zsdycs/ginpun/kb84/1. 成品图片/KB84-1.jpg

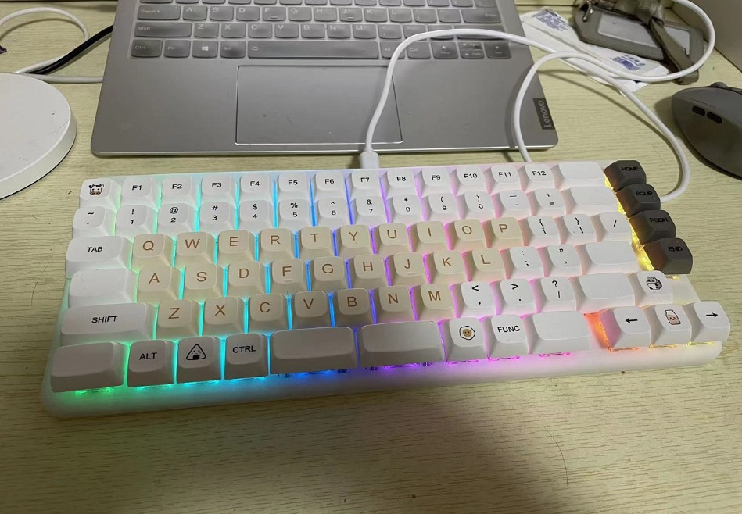
kb84/1. 成品图片/KB84-1.jpg
