zsdycs/ginpun/kb84/1. 成品图片/KB84-2.jpg

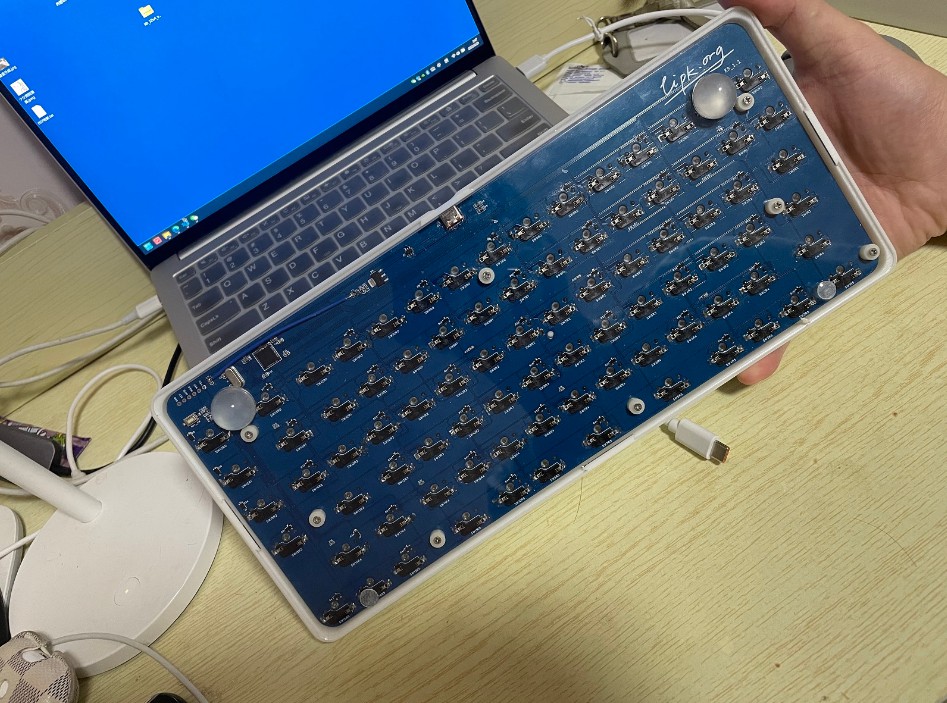
kb84/1. 成品图片/KB84-2.jpg
