zsdycs/ginpun/kb84/1. 成品图片/KB84-5.jpg

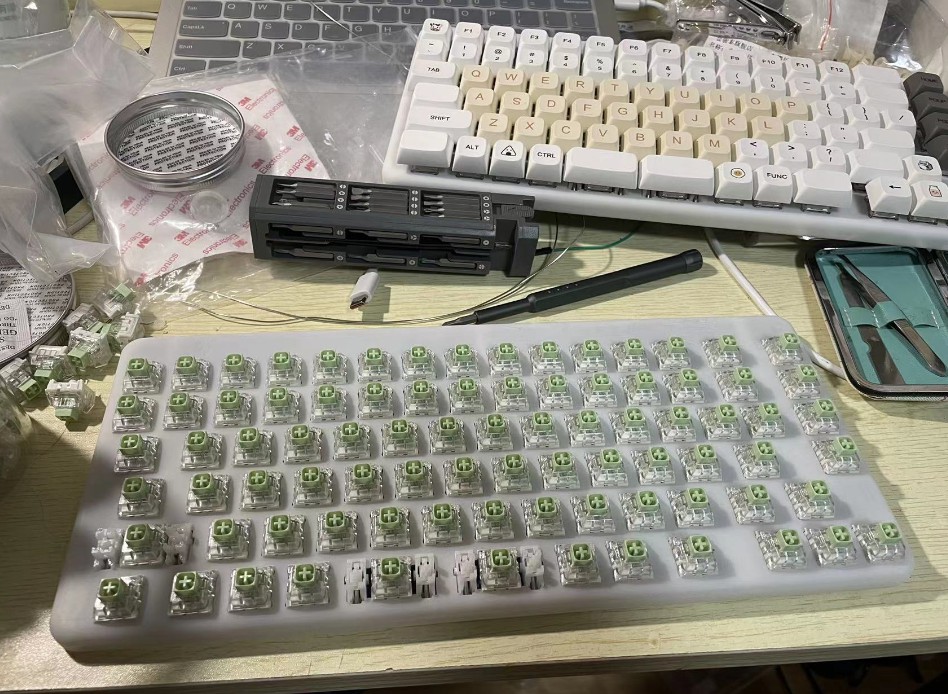
kb84/1. 成品图片/KB84-5.jpg
