zsdycs/ginpun/kb84/3. 原理图/SCH_kb_32u4_v1.3_P2.png

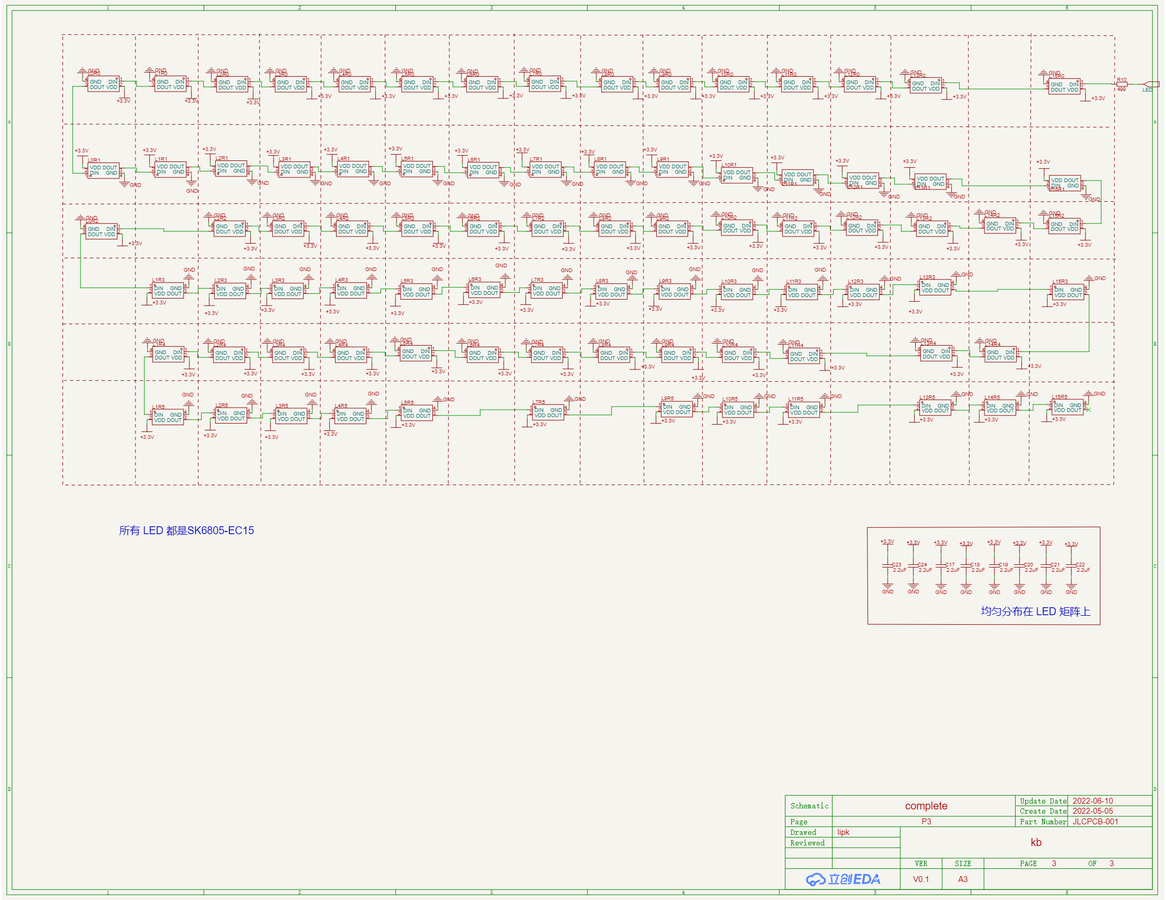
kb84/3. 原理图/SCH_kb_32u4_v1.3_P2.png
