zsdycs/ginpun/kb84/4. 电路板/kb_32u4_v1.3_top.png

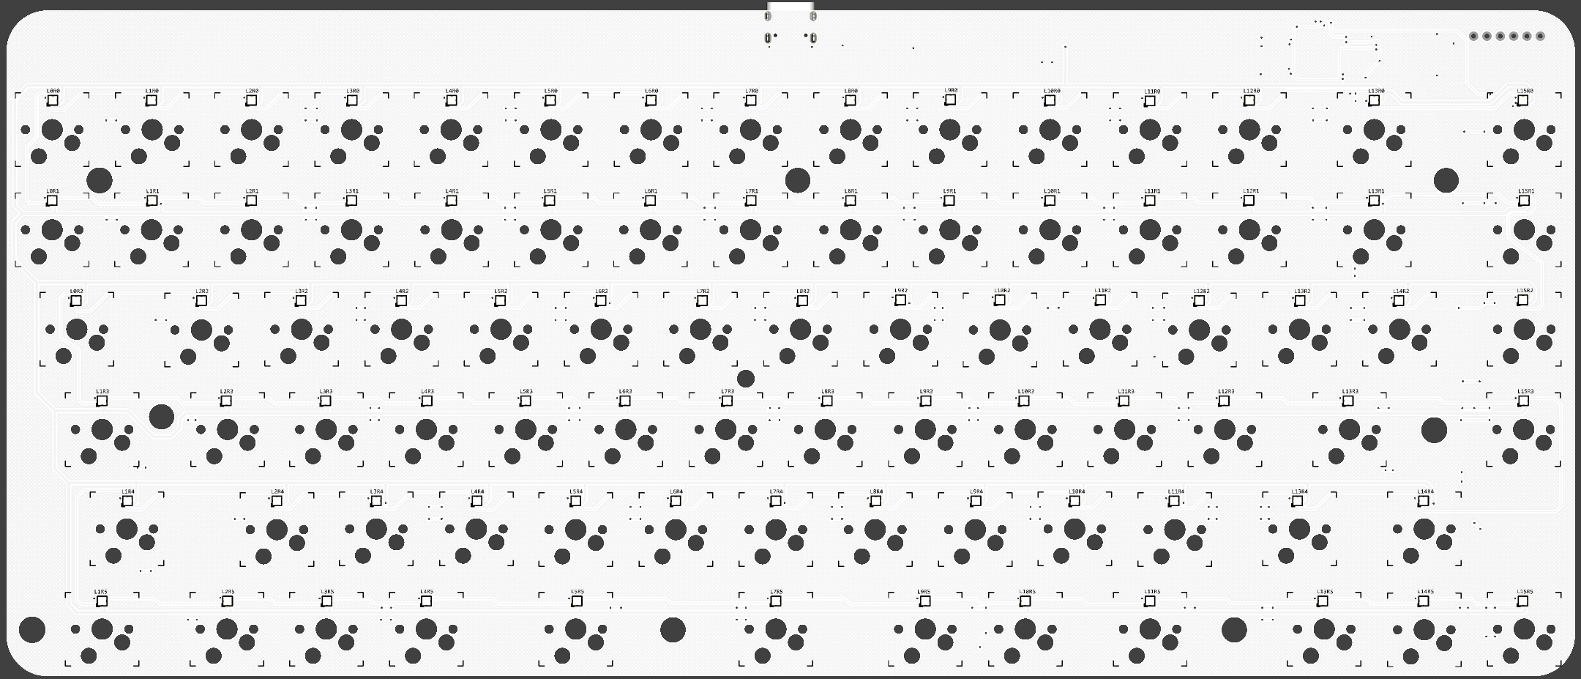
kb84/4. 电路板/kb_32u4_v1.3_top.png
