zsdycs/ginpun/kb84/键盘设计文件/keyboard-Layer 1.jpg

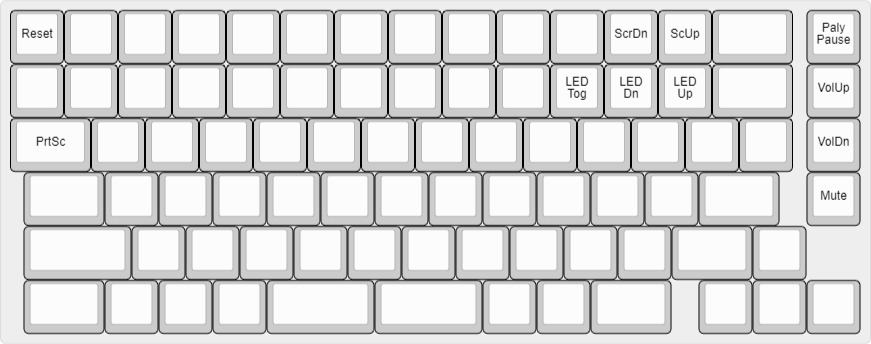
kb84/键盘设计文件/keyboard-Layer 1.jpg
