zsdycs/ginpun/kb84/键盘设计文件/键盘矩阵布线.jpg

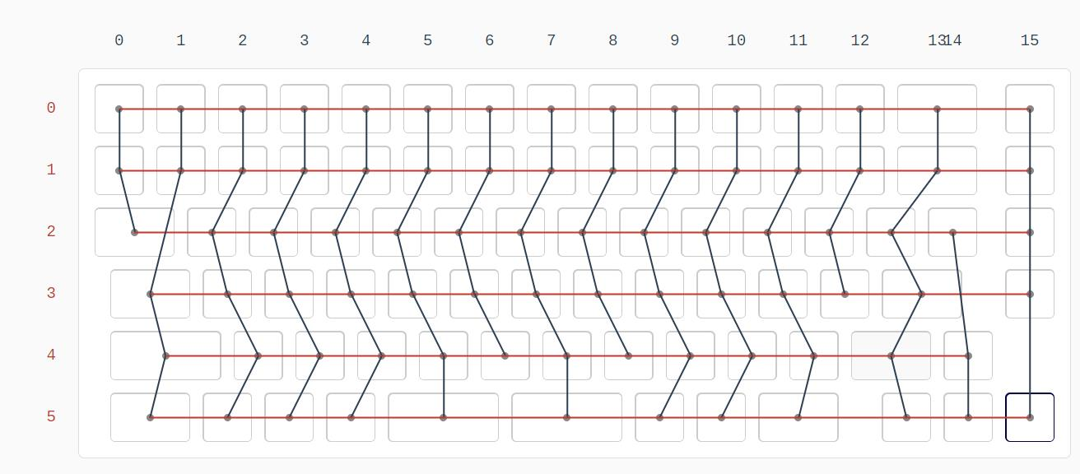
kb84/键盘设计文件/键盘矩阵布线.jpg
