zsdycs/ginpun/sg_v2/4. 电路板/PCB_buttom.png

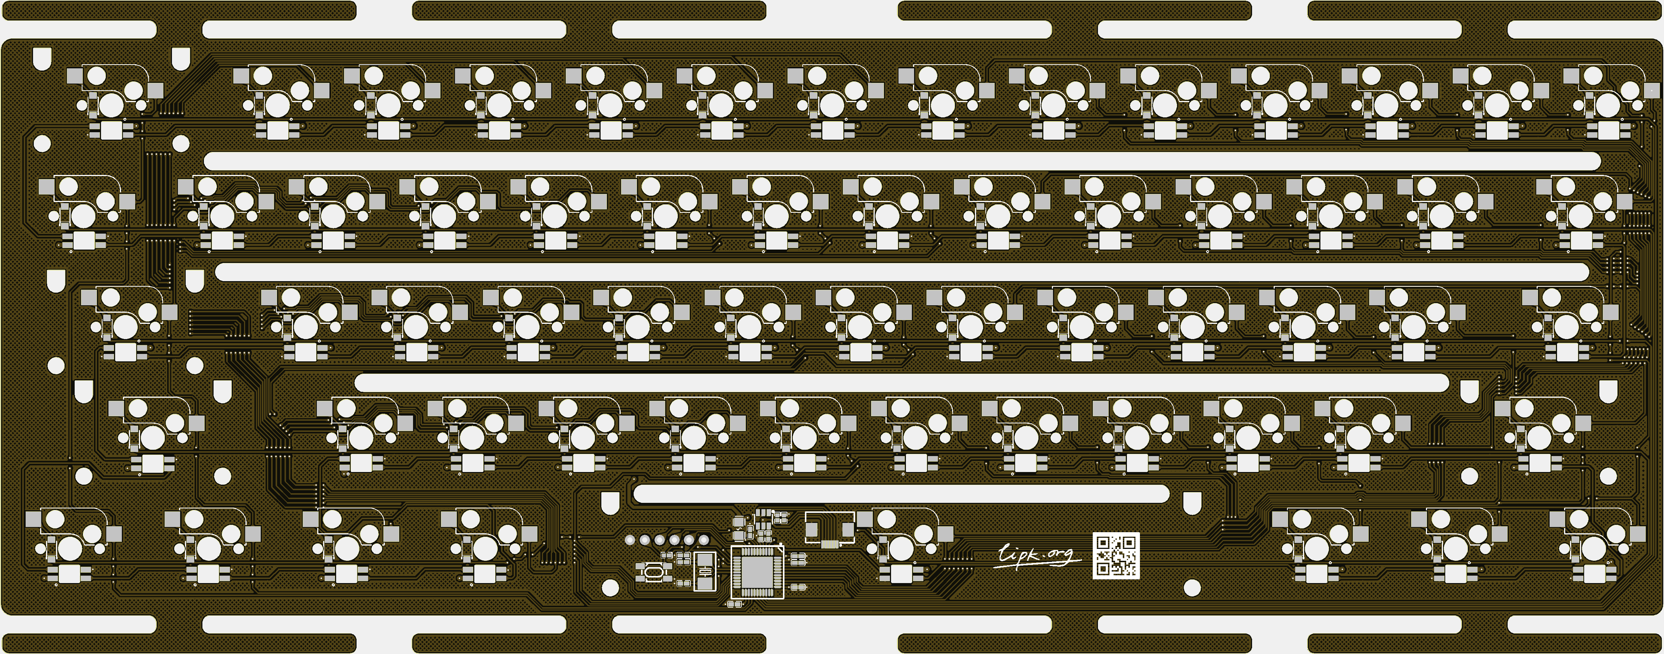
sg_v2/4. 电路板/PCB_buttom.png
