zsdycs/ginpun/sg_v2/4. 电路板/PCB_top.png

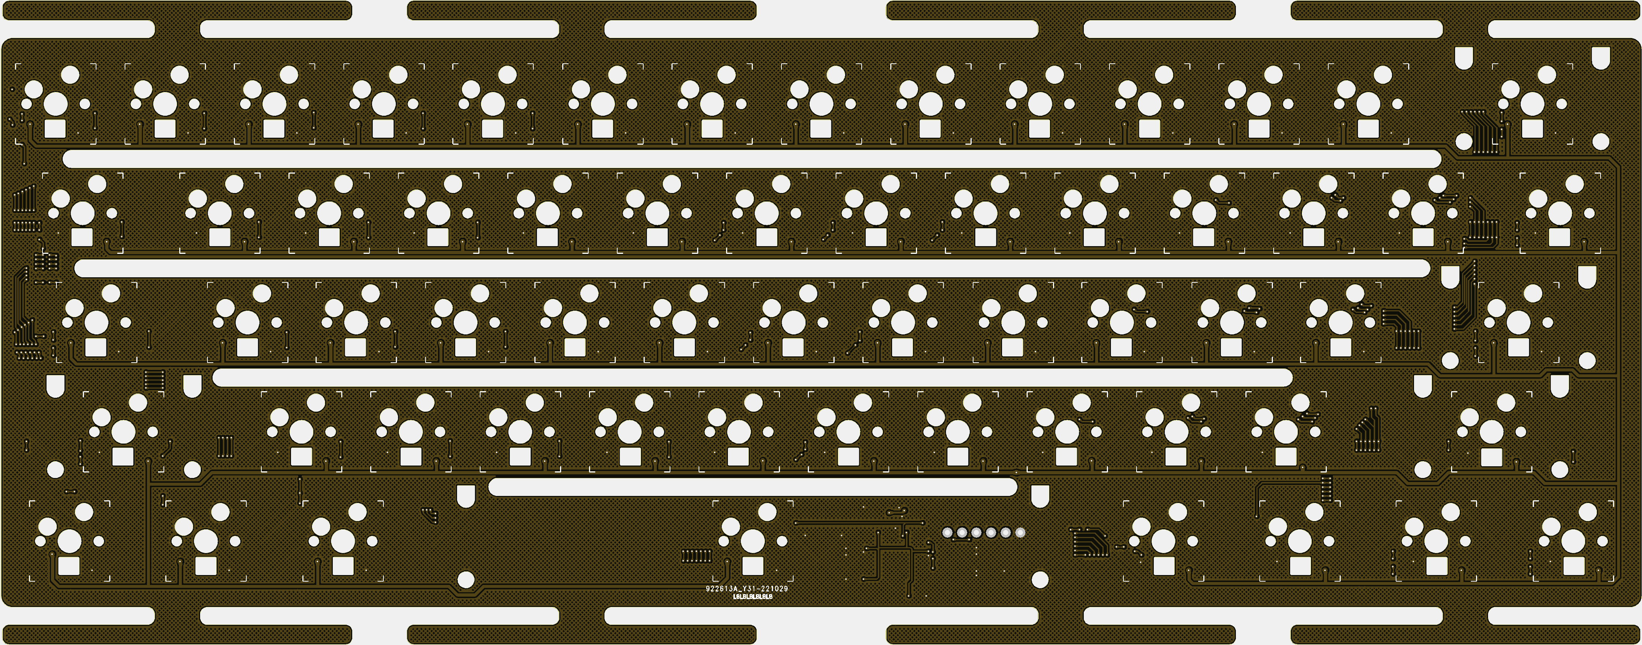
sg_v2/4. 电路板/PCB_top.png
