zsdycs/ginpun/sg_v2/4. 电路板/SG61线路矩阵.jpg

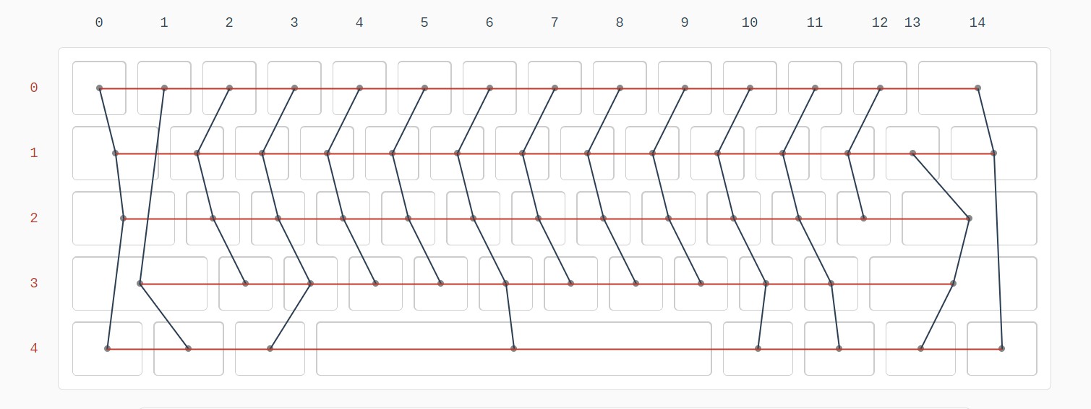
sg_v2/4. 电路板/SG61线路矩阵.jpg
