zsdycs/ginpun/sg_v2/键盘设计文件/矩阵配列/sg2-0_68/sg2-0_68.jpg

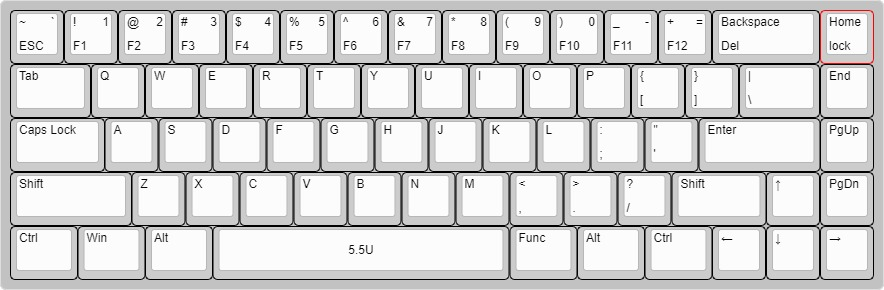
sg_v2/键盘设计文件/矩阵配列/sg2-0_68/sg2-0_68.jpg
