zsdycs/ginpun/通用资料/m32a熔丝位.jpg

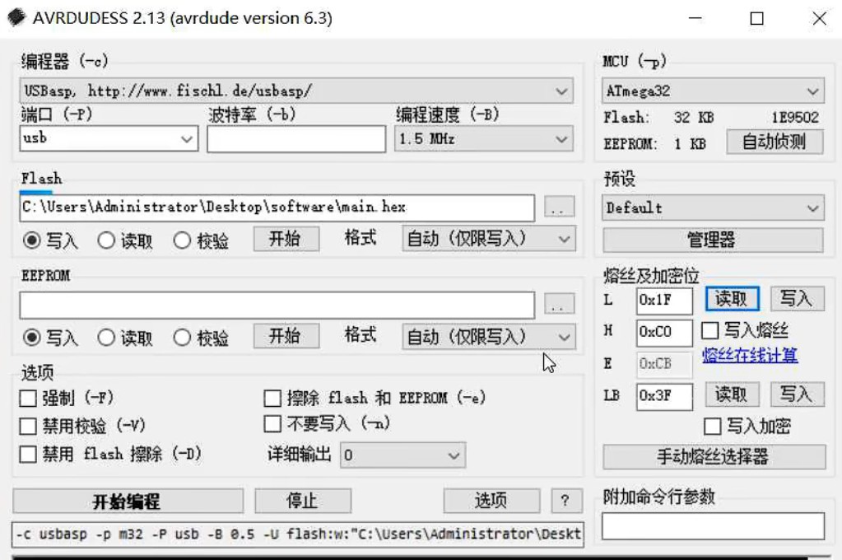
通用资料/m32a熔丝位.jpg
