zsdycs/ginpun/通用资料/usbASP烧录器接线.jpg

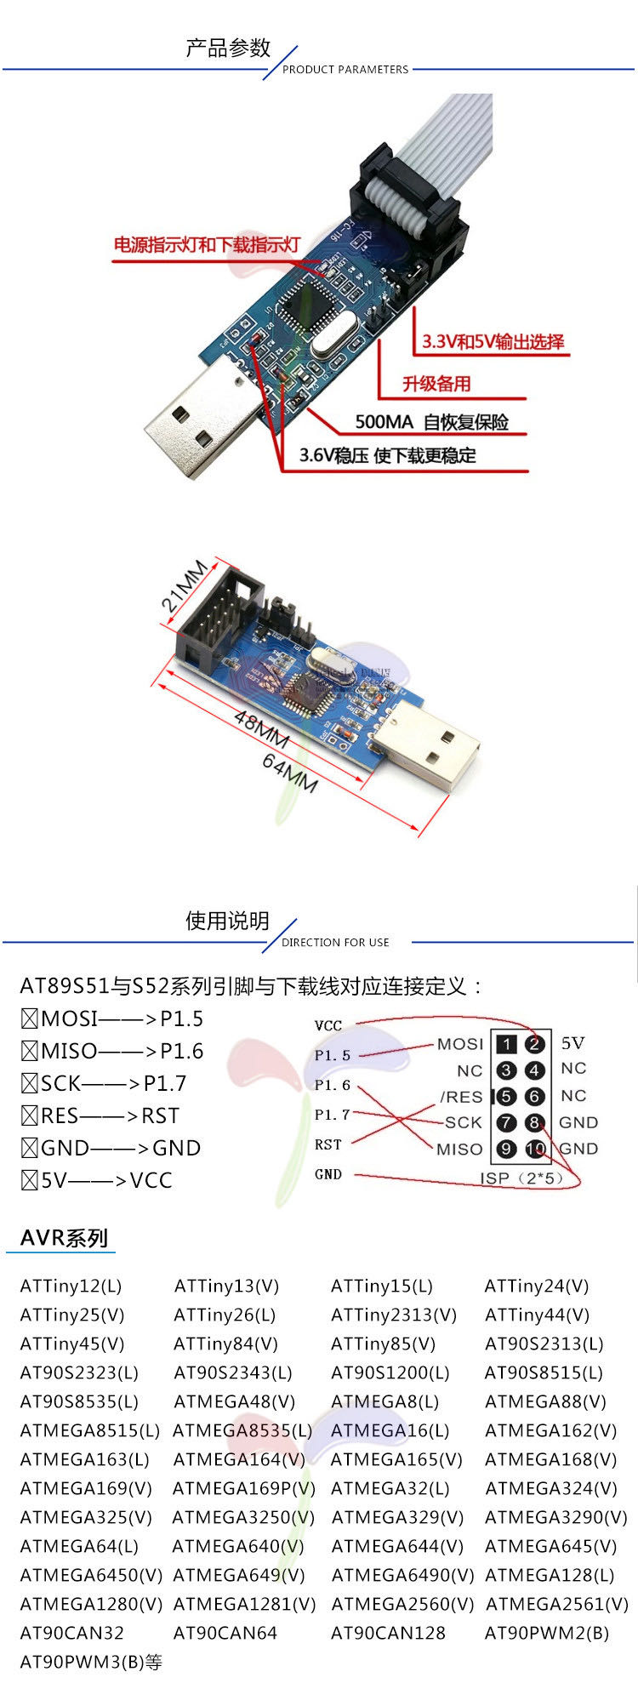
通用资料/usbASP烧录器接线.jpg
