zsdycs/ginpun/kb84/2. 机械结构/外壳 v1/pillar.step

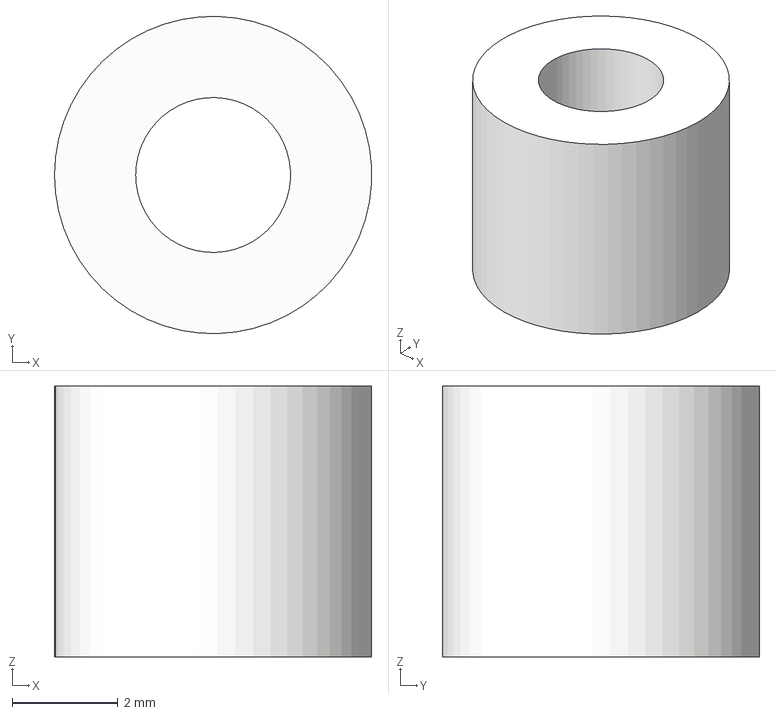
[picture p47: CAD file, 2022-06-17, an earlier design]
kb84/2. 机械结构/外壳 v1/pillar.step
6.00 x 6.00 x 5.12 mm
