zsdycs/ginpun/sg_v2/键盘设计文件/定位板/sg2-0_83/builder.swillkb.com.png

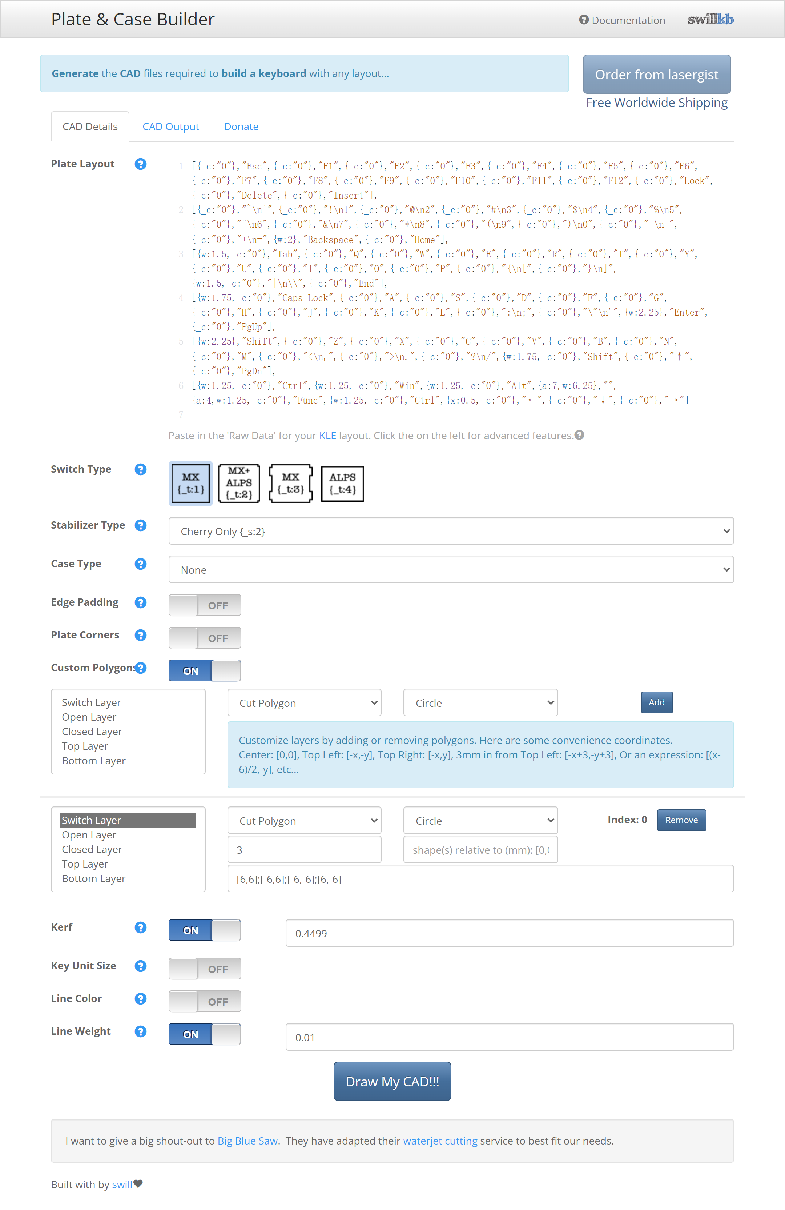
sg_v2/键盘设计文件/定位板/sg2-0_83/builder.swillkb.com.png
